jeffc/nrf52-watch-obsolete/packages/framework-arduinoadafruitnrf52/cores/nRF5/nordic/nrfx/mdk/nrf51_to_nrf52.h

/*

Copyright (c) 2010 - 2018, Nordic Semiconductor ASA All rights reserved.

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
1. Redistributions of source code must retain the above copyright notice, this
   list of conditions and the following disclaimer.

2. Redistributions in binary form must reproduce the above copyright
   notice, this list of conditions and the following disclaimer in the
   documentation and/or other materials provided with the distribution.

3. Neither the name of Nordic Semiconductor ASA nor the names of its
   contributors may be used to endorse or promote products derived from this
   software without specific prior written permission.

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
*/

#ifndef NRF51_TO_NRF52_H
#define NRF51_TO_NRF52_H

/*lint ++flb "Enter library region */

/* This file is given to prevent your SW from not compiling with the name changes between nRF51 and nRF52 devices.
 * It redefines the old nRF51 names into the new ones as long as the functionality is still supported. If the
 * functionality is gone, there old names are not defined, so compilation will fail. Note that also includes macros
 * from the nrf51_deprecated.h file. */


/* IRQ */
/* Several peripherals have been added to several indexes. Names of IRQ handlers and IRQ numbers have changed. */
#ifndef UART0_IRQHandler
    #define UART0_IRQHandler        UARTE0_UART0_IRQHandler
#endif
#ifndef SPI0_TWI0_IRQHandler
    #define SPI0_TWI0_IRQHandler    SPIM0_SPIS0_TWIM0_TWIS0_SPI0_TWI0_IRQHandler
#endif
#ifndef SPI1_TWI1_IRQHandler
    #define SPI1_TWI1_IRQHandler    SPIM1_SPIS1_TWIM1_TWIS1_SPI1_TWI1_IRQHandler
#endif
#ifndef ADC_IRQHandler
    #define ADC_IRQHandler          SAADC_IRQHandler
#endif
#ifndef LPCOMP_IRQHandler
    #define LPCOMP_IRQHandler       COMP_LPCOMP_IRQHandler
#endif
#ifndef SWI0_IRQHandler
    #define SWI0_IRQHandler         SWI0_EGU0_IRQHandler
#endif
#ifndef SWI1_IRQHandler
    #define SWI1_IRQHandler         SWI1_EGU1_IRQHandler
#endif
#ifndef SWI2_IRQHandler
    #define SWI2_IRQHandler         SWI2_EGU2_IRQHandler
#endif
#ifndef SWI3_IRQHandler
    #define SWI3_IRQHandler         SWI3_EGU3_IRQHandler
#endif
#ifndef SWI4_IRQHandler
    #define SWI4_IRQHandler         SWI4_EGU4_IRQHandler
#endif
#ifndef SWI5_IRQHandler
    #define SWI5_IRQHandler         SWI5_EGU5_IRQHandler
#endif

#ifndef UART0_IRQn
    #define UART0_IRQn              UARTE0_UART0_IRQn
#endif
#ifndef SPI0_TWI0_IRQn
    #define SPI0_TWI0_IRQn          SPIM0_SPIS0_TWIM0_TWIS0_SPI0_TWI0_IRQn
#endif
#ifndef SPI1_TWI1_IRQn
    #define SPI1_TWI1_IRQn          SPIM1_SPIS1_TWIM1_TWIS1_SPI1_TWI1_IRQn
#endif
#ifndef ADC_IRQn
    #define ADC_IRQn                SAADC_IRQn
#endif
#ifndef LPCOMP_IRQn
    #define LPCOMP_IRQn             COMP_LPCOMP_IRQn
#endif
#ifndef SWI0_IRQn
    #define SWI0_IRQn               SWI0_EGU0_IRQn
#endif
#ifndef SWI1_IRQn
    #define SWI1_IRQn               SWI1_EGU1_IRQn
#endif
#ifndef SWI2_IRQn
    #define SWI2_IRQn               SWI2_EGU2_IRQn
#endif
#ifndef SWI3_IRQn
    #define SWI3_IRQn               SWI3_EGU3_IRQn
#endif    
#ifndef SWI4_IRQn
    #define SWI4_IRQn               SWI4_EGU4_IRQn
#endif    
#ifndef SWI5_IRQn
    #define SWI5_IRQn               SWI5_EGU5_IRQn
#endif


/* UICR */
/* Register RBPCONF was renamed to APPROTECT. */
#ifndef RBPCONF
    #define RBPCONF     APPROTECT
#endif

#ifndef UICR_RBPCONF_PALL_Pos
    #define UICR_RBPCONF_PALL_Pos           UICR_APPROTECT_PALL_Pos
#endif
#ifndef UICR_RBPCONF_PALL_Msk
    #define UICR_RBPCONF_PALL_Msk           UICR_APPROTECT_PALL_Msk
#endif
#ifndef UICR_RBPCONF_PALL_Enabled
    #define UICR_RBPCONF_PALL_Enabled       UICR_APPROTECT_PALL_Enabled
#endif
#ifndef UICR_RBPCONF_PALL_Disabled
    #define UICR_RBPCONF_PALL_Disabled      UICR_APPROTECT_PALL_Disabled
#endif

/* GPIO */
/* GPIO port was renamed to P0. */
#ifndef NRF_GPIO
    #define NRF_GPIO        NRF_P0
#endif
#ifndef NRF_GPIO_BASE
    #define NRF_GPIO_BASE   NRF_P0_BASE
#endif

/* QDEC */
/* The registers PSELA, PSELB and PSELLED were restructured into a struct. */
#ifndef PSELLED
    #define PSELLED     PSEL.LED
#endif
#ifndef PSELA
    #define PSELA       PSEL.A
#endif
#ifndef PSELB
    #define PSELB       PSEL.B
#endif


/* SPIS */
/* The registers PSELSCK, PSELMISO, PSELMOSI, PSELCSN were restructured into a struct. */
#ifndef PSELSCK
    #define PSELSCK       PSEL.SCK
#endif
#ifndef PSELMISO
    #define PSELMISO      PSEL.MISO
#endif
#ifndef PSELMOSI
    #define PSELMOSI      PSEL.MOSI
#endif
#ifndef PSELCSN
    #define PSELCSN       PSEL.CSN
#endif    

/* The registers RXDPTR, MAXRX, AMOUNTRX were restructured into a struct */
#ifndef RXDPTR
    #define RXDPTR        RXD.PTR
#endif
#ifndef MAXRX
    #define MAXRX         RXD.MAXCNT
#endif
#ifndef AMOUNTRX
    #define AMOUNTRX      RXD.AMOUNT
#endif

#ifndef SPIS_MAXRX_MAXRX_Pos
    #define SPIS_MAXRX_MAXRX_Pos        SPIS_RXD_MAXCNT_MAXCNT_Pos
#endif
#ifndef SPIS_MAXRX_MAXRX_Msk
    #define SPIS_MAXRX_MAXRX_Msk        SPIS_RXD_MAXCNT_MAXCNT_Msk
#endif

#ifndef SPIS_AMOUNTRX_AMOUNTRX_Pos
    #define SPIS_AMOUNTRX_AMOUNTRX_Pos  SPIS_RXD_AMOUNT_AMOUNT_Pos
#endif
#ifndef SPIS_AMOUNTRX_AMOUNTRX_Msk
    #define SPIS_AMOUNTRX_AMOUNTRX_Msk  SPIS_RXD_AMOUNT_AMOUNT_Msk
#endif

/* The registers TXDPTR, MAXTX, AMOUNTTX were restructured into a struct */
#ifndef TXDPTR
    #define TXDPTR        TXD.PTR
#endif
#ifndef MAXTX
    #define MAXTX         TXD.MAXCNT
#endif
#ifndef AMOUNTTX
    #define AMOUNTTX      TXD.AMOUNT
#endif

#ifndef SPIS_MAXTX_MAXTX_Pos
    #define SPIS_MAXTX_MAXTX_Pos        SPIS_TXD_MAXCNT_MAXCNT_Pos
#endif
#ifndef SPIS_MAXTX_MAXTX_Msk
    #define SPIS_MAXTX_MAXTX_Msk        SPIS_TXD_MAXCNT_MAXCNT_Msk
#endif

#ifndef SPIS_AMOUNTTX_AMOUNTTX_Pos
    #define SPIS_AMOUNTTX_AMOUNTTX_Pos  SPIS_TXD_AMOUNT_AMOUNT_Pos
#endif
#ifndef SPIS_AMOUNTTX_AMOUNTTX_Msk
    #define SPIS_AMOUNTTX_AMOUNTTX_Msk  SPIS_TXD_AMOUNT_AMOUNT_Msk
#endif

/* MPU */
/* Part of MPU module was renamed BPROT, while the rest was eliminated. */
#ifndef NRF_MPU
    #define NRF_MPU     NRF_BPROT
#endif

/* Register DISABLEINDEBUG macros were affected. */
#ifndef MPU_DISABLEINDEBUG_DISABLEINDEBUG_Pos
    #define MPU_DISABLEINDEBUG_DISABLEINDEBUG_Pos       BPROT_DISABLEINDEBUG_DISABLEINDEBUG_Pos
#endif
#ifndef MPU_DISABLEINDEBUG_DISABLEINDEBUG_Msk
    #define MPU_DISABLEINDEBUG_DISABLEINDEBUG_Msk       BPROT_DISABLEINDEBUG_DISABLEINDEBUG_Msk
#endif
#ifndef MPU_DISABLEINDEBUG_DISABLEINDEBUG_Enabled
    #define MPU_DISABLEINDEBUG_DISABLEINDEBUG_Enabled   BPROT_DISABLEINDEBUG_DISABLEINDEBUG_Enabled
#endif
#ifndef MPU_DISABLEINDEBUG_DISABLEINDEBUG_Disabled
    #define MPU_DISABLEINDEBUG_DISABLEINDEBUG_Disabled  BPROT_DISABLEINDEBUG_DISABLEINDEBUG_Disabled
#endif

/* Registers PROTENSET0 and PROTENSET1 were affected and renamed as CONFIG0 and CONFIG1. */
#ifndef PROTENSET0
    #define PROTENSET0  CONFIG0
#endif
#ifndef PROTENSET1
    #define PROTENSET1  CONFIG1
#endif

#ifndef MPU_PROTENSET1_PROTREG63_Pos
    #define MPU_PROTENSET1_PROTREG63_Pos        BPROT_CONFIG1_REGION63_Pos
#endif
#ifndef MPU_PROTENSET1_PROTREG63_Msk
    #define MPU_PROTENSET1_PROTREG63_Msk        BPROT_CONFIG1_REGION63_Msk
#endif
#ifndef MPU_PROTENSET1_PROTREG63_Disabled
    #define MPU_PROTENSET1_PROTREG63_Disabled   BPROT_CONFIG1_REGION63_Disabled
#endif
#ifndef MPU_PROTENSET1_PROTREG63_Enabled
    #define MPU_PROTENSET1_PROTREG63_Enabled    BPROT_CONFIG1_REGION63_Enabled
#endif
#ifndef MPU_PROTENSET1_PROTREG63_Set
    #define MPU_PROTENSET1_PROTREG63_Set        BPROT_CONFIG1_REGION63_Enabled
#endif

#ifndef MPU_PROTENSET1_PROTREG62_Pos
    #define MPU_PROTENSET1_PROTREG62_Pos        BPROT_CONFIG1_REGION62_Pos
#endif
#ifndef MPU_PROTENSET1_PROTREG62_Msk
    #define MPU_PROTENSET1_PROTREG62_Msk        BPROT_CONFIG1_REGION62_Msk
#endif
#ifndef MPU_PROTENSET1_PROTREG62_Disabled
    #define MPU_PROTENSET1_PROTREG62_Disabled   BPROT_CONFIG1_REGION62_Disabled
#endif
#ifndef MPU_PROTENSET1_PROTREG62_Enabled
    #define MPU_PROTENSET1_PROTREG62_Enabled    BPROT_CONFIG1_REGION62_Enabled
#endif
#ifndef MPU_PROTENSET1_PROTREG62_Set
    #define MPU_PROTENSET1_PROTREG62_Set        BPROT_CONFIG1_REGION62_Enabled
#endif

#ifndef MPU_PROTENSET1_PROTREG61_Pos
    #define MPU_PROTENSET1_PROTREG61_Pos        BPROT_CONFIG1_REGION61_Pos
#endif
#ifndef MPU_PROTENSET1_PROTREG61_Msk
    #define MPU_PROTENSET1_PROTREG61_Msk        BPROT_CONFIG1_REGION61_Msk
#endif
#ifndef MPU_PROTENSET1_PROTREG61_Disabled
    #define MPU_PROTENSET1_PROTREG61_Disabled   BPROT_CONFIG1_REGION61_Disabled
#endif
#ifndef MPU_PROTENSET1_PROTREG61_Enabled
    #define MPU_PROTENSET1_PROTREG61_Enabled    BPROT_CONFIG1_REGION61_Enabled
#endif
#ifndef MPU_PROTENSET1_PROTREG61_Set
    #define MPU_PROTENSET1_PROTREG61_Set        BPROT_CONFIG1_REGION61_Enabled
#endif

#ifndef MPU_PROTENSET1_PROTREG60_Pos
    #define MPU_PROTENSET1_PROTREG60_Pos        BPROT_CONFIG1_REGION60_Pos
#endif
#ifndef MPU_PROTENSET1_PROTREG60_Msk
    #define MPU_PROTENSET1_PROTREG60_Msk        BPROT_CONFIG1_REGION60_Msk
#endif
#ifndef MPU_PROTENSET1_PROTREG60_Disabled
    #define MPU_PROTENSET1_PROTREG60_Disabled   BPROT_CONFIG1_REGION60_Disabled
#endif
#ifndef MPU_PROTENSET1_PROTREG60_Enabled
    #define MPU_PROTENSET1_PROTREG60_Enabled    BPROT_CONFIG1_REGION60_Enabled
#endif
#ifndef MPU_PROTENSET1_PROTREG60_Set
    #define MPU_PROTENSET1_PROTREG60_Set        BPROT_CONFIG1_REGION60_Enabled
#endif

#ifndef MPU_PROTENSET1_PROTREG59_Pos
    #define MPU_PROTENSET1_PROTREG59_Pos        BPROT_CONFIG1_REGION59_Pos
#endif
#ifndef MPU_PROTENSET1_PROTREG59_Msk
    #define MPU_PROTENSET1_PROTREG59_Msk        BPROT_CONFIG1_REGION59_Msk
#endif
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
#endif
#ifndef MPU_PROTENSET0_PROTREG2_Enabled
    #define MPU_PROTENSET0_PROTREG2_Enabled    BPROT_CONFIG0_REGION2_Enabled
#endif
#ifndef MPU_PROTENSET0_PROTREG2_Set
    #define MPU_PROTENSET0_PROTREG2_Set        BPROT_CONFIG0_REGION2_Enabled
#endif

#ifndef MPU_PROTENSET0_PROTREG1_Pos
    #define MPU_PROTENSET0_PROTREG1_Pos        BPROT_CONFIG0_REGION1_Pos
#endif
#ifndef MPU_PROTENSET0_PROTREG1_Msk
    #define MPU_PROTENSET0_PROTREG1_Msk        BPROT_CONFIG0_REGION1_Msk
#endif
#ifndef MPU_PROTENSET0_PROTREG1_Disabled
    #define MPU_PROTENSET0_PROTREG1_Disabled   BPROT_CONFIG0_REGION1_Disabled
#endif
#ifndef MPU_PROTENSET0_PROTREG1_Enabled
    #define MPU_PROTENSET0_PROTREG1_Enabled    BPROT_CONFIG0_REGION1_Enabled
#endif
#ifndef MPU_PROTENSET0_PROTREG1_Set
    #define MPU_PROTENSET0_PROTREG1_Set        BPROT_CONFIG0_REGION1_Enabled
#endif

#ifndef MPU_PROTENSET0_PROTREG0_Pos
    #define MPU_PROTENSET0_PROTREG0_Pos        BPROT_CONFIG0_REGION0_Pos
#endif
#ifndef MPU_PROTENSET0_PROTREG0_Msk
    #define MPU_PROTENSET0_PROTREG0_Msk        BPROT_CONFIG0_REGION0_Msk
#endif
#ifndef MPU_PROTENSET0_PROTREG0_Disabled
    #define MPU_PROTENSET0_PROTREG0_Disabled   BPROT_CONFIG0_REGION0_Disabled
#endif
#ifndef MPU_PROTENSET0_PROTREG0_Enabled
    #define MPU_PROTENSET0_PROTREG0_Enabled    BPROT_CONFIG0_REGION0_Enabled
#endif
#ifndef MPU_PROTENSET0_PROTREG0_Set
    #define MPU_PROTENSET0_PROTREG0_Set        BPROT_CONFIG0_REGION0_Enabled
#endif


/* From nrf51_deprecated.h */

/* NVMC */
/* The register ERASEPROTECTEDPAGE changed name to ERASEPCR0 in the documentation. */
#ifndef ERASEPROTECTEDPAGE
    #define ERASEPROTECTEDPAGE      ERASEPCR0
#endif    


/* IRQ */
/* COMP module was eliminated. Adapted to nrf52 headers. */
#ifndef LPCOMP_COMP_IRQHandler
    #define LPCOMP_COMP_IRQHandler  COMP_LPCOMP_IRQHandler
#endif
#ifndef LPCOMP_COMP_IRQn
    #define LPCOMP_COMP_IRQn        COMP_LPCOMP_IRQn
#endif


/* REFSEL register redefined enumerated values and added some more. */
#ifndef LPCOMP_REFSEL_REFSEL_SupplyOneEighthPrescaling
    #define LPCOMP_REFSEL_REFSEL_SupplyOneEighthPrescaling          LPCOMP_REFSEL_REFSEL_Ref1_8Vdd
#endif
#ifndef LPCOMP_REFSEL_REFSEL_SupplyTwoEighthsPrescaling
    #define LPCOMP_REFSEL_REFSEL_SupplyTwoEighthsPrescaling         LPCOMP_REFSEL_REFSEL_Ref2_8Vdd
#endif
#ifndef LPCOMP_REFSEL_REFSEL_SupplyThreeEighthsPrescaling
    #define LPCOMP_REFSEL_REFSEL_SupplyThreeEighthsPrescaling       LPCOMP_REFSEL_REFSEL_Ref3_8Vdd
#endif
#ifndef LPCOMP_REFSEL_REFSEL_SupplyFourEighthsPrescaling
    #define LPCOMP_REFSEL_REFSEL_SupplyFourEighthsPrescaling        LPCOMP_REFSEL_REFSEL_Ref4_8Vdd
#endif
#ifndef LPCOMP_REFSEL_REFSEL_SupplyFiveEighthsPrescaling
    #define LPCOMP_REFSEL_REFSEL_SupplyFiveEighthsPrescaling        LPCOMP_REFSEL_REFSEL_Ref5_8Vdd
#endif
#ifndef LPCOMP_REFSEL_REFSEL_SupplySixEighthsPrescaling
    #define LPCOMP_REFSEL_REFSEL_SupplySixEighthsPrescaling         LPCOMP_REFSEL_REFSEL_Ref6_8Vdd
#endif
#ifndef LPCOMP_REFSEL_REFSEL_SupplySevenEighthsPrescaling
    #define LPCOMP_REFSEL_REFSEL_SupplySevenEighthsPrescaling       LPCOMP_REFSEL_REFSEL_Ref7_8Vdd
#endif

/* RADIO */
/* The name of the field SKIPADDR was corrected. Old macros added for compatibility. */
#ifndef RADIO_CRCCNF_SKIP_ADDR_Pos
    #define RADIO_CRCCNF_SKIP_ADDR_Pos      RADIO_CRCCNF_SKIPADDR_Pos
#endif
#ifndef RADIO_CRCCNF_SKIP_ADDR_Msk
    #define RADIO_CRCCNF_SKIP_ADDR_Msk      RADIO_CRCCNF_SKIPADDR_Msk
#endif
#ifndef RADIO_CRCCNF_SKIP_ADDR_Include
    #define RADIO_CRCCNF_SKIP_ADDR_Include  RADIO_CRCCNF_SKIPADDR_Include
#endif
#ifndef RADIO_CRCCNF_SKIP_ADDR_Skip
    #define RADIO_CRCCNF_SKIP_ADDR_Skip     RADIO_CRCCNF_SKIPADDR_Skip
#endif


/* FICR */
/* The registers FICR.DEVICEID0 and FICR.DEVICEID1 were renamed into an array. */
#ifndef DEVICEID0
    #define DEVICEID0       DEVICEID[0]
#endif
#ifndef DEVICEID1
    #define DEVICEID1       DEVICEID[1]
#endif

/* The registers FICR.ER0, FICR.ER1, FICR.ER2 and FICR.ER3 were renamed into an array. */
#ifndef ER0
    #define ER0             ER[0]
#endif
#ifndef ER1
    #define ER1             ER[1]
#endif
#ifndef ER2
    #define ER2             ER[2]
#endif
#ifndef ER3
    #define ER3             ER[3]
#endif

/* The registers FICR.IR0, FICR.IR1, FICR.IR2 and FICR.IR3 were renamed into an array. */
#ifndef IR0
    #define IR0             IR[0]
#endif
#ifndef IR1
    #define IR1             IR[1]
#endif
#ifndef IR2
    #define IR2             IR[2]
#endif
#ifndef IR3
    #define IR3             IR[3]
#endif

/* The registers FICR.DEVICEADDR0 and FICR.DEVICEADDR1 were renamed into an array. */
#ifndef DEVICEADDR0
    #define DEVICEADDR0     DEVICEADDR[0]
#endif
#ifndef DEVICEADDR1
    #define DEVICEADDR1     DEVICEADDR[1]
#endif


/* PPI */
/* The tasks PPI.TASKS_CHGxEN and PPI.TASKS_CHGxDIS were renamed into an array of structs. */
#ifndef TASKS_CHG0EN
    #define TASKS_CHG0EN     TASKS_CHG[0].EN
#endif
#ifndef TASKS_CHG0DIS
    #define TASKS_CHG0DIS    TASKS_CHG[0].DIS
#endif
#ifndef TASKS_CHG1EN
    #define TASKS_CHG1EN     TASKS_CHG[1].EN
#endif
#ifndef TASKS_CHG1DIS
    #define TASKS_CHG1DIS    TASKS_CHG[1].DIS
#endif
#ifndef TASKS_CHG2EN
    #define TASKS_CHG2EN     TASKS_CHG[2].EN
#endif
#ifndef TASKS_CHG2DIS
    #define TASKS_CHG2DIS    TASKS_CHG[2].DIS
#endif
#ifndef TASKS_CHG3EN
    #define TASKS_CHG3EN     TASKS_CHG[3].EN
#endif
#ifndef TASKS_CHG3DIS
    #define TASKS_CHG3DIS    TASKS_CHG[3].DIS
#endif

/* The registers PPI.CHx_EEP and PPI.CHx_TEP were renamed into an array of structs. */
#ifndef CH0_EEP
    #define CH0_EEP          CH[0].EEP
#endif
#ifndef CH0_TEP
    #define CH0_TEP          CH[0].TEP
#endif
#ifndef CH1_EEP
    #define CH1_EEP          CH[1].EEP
#endif
#ifndef CH1_TEP
    #define CH1_TEP          CH[1].TEP
#endif
#ifndef CH2_EEP
    #define CH2_EEP          CH[2].EEP
#endif
#ifndef CH2_TEP
    #define CH2_TEP          CH[2].TEP
#endif
#ifndef CH3_EEP
    #define CH3_EEP          CH[3].EEP
#endif
#ifndef CH3_TEP
    #define CH3_TEP          CH[3].TEP
#endif
#ifndef CH4_EEP
    #define CH4_EEP          CH[4].EEP
#endif
#ifndef CH4_TEP
    #define CH4_TEP          CH[4].TEP
#endif
#ifndef CH5_EEP
    #define CH5_EEP          CH[5].EEP
#endif
#ifndef CH5_TEP
    #define CH5_TEP          CH[5].TEP
#endif
#ifndef CH6_EEP
    #define CH6_EEP          CH[6].EEP
#endif
#ifndef CH6_TEP
    #define CH6_TEP          CH[6].TEP
#endif 
#ifndef CH7_EEP
    #define CH7_EEP          CH[7].EEP
#endif
#ifndef CH7_TEP
    #define CH7_TEP          CH[7].TEP
#endif
#ifndef CH8_EEP
    #define CH8_EEP          CH[8].EEP
#endif
#ifndef CH8_TEP
    #define CH8_TEP          CH[8].TEP
#endif
#ifndef CH9_EEP
    #define CH9_EEP          CH[9].EEP
#endif
#ifndef CH9_TEP
    #define CH9_TEP          CH[9].TEP
#endif
#ifndef CH10_EEP
    #define CH10_EEP         CH[10].EEP
#endif
#ifndef CH10_TEP
    #define CH10_TEP         CH[10].TEP
#endif
#ifndef CH11_EEP
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
#endif
#ifndef PPI_CHG3_CH0_Excluded
    #define PPI_CHG3_CH0_Excluded   PPI_CHG_CH0_Excluded
#endif
#ifndef PPI_CHG3_CH0_Included
    #define PPI_CHG3_CH0_Included   PPI_CHG_CH0_Included
#endif



/*lint --flb "Leave library region" */

#endif /* NRF51_TO_NRF52_H */
