jeffc/nrf52-watch-obsolete/packages/framework-arduinoadafruitnrf52/cores/nRF5/nordic/softdevice/s132_nrf52_6.1.1_API/include/ble_gap.h

/*
 * Copyright (c) 2011 - 2018, Nordic Semiconductor ASA
 * All rights reserved.
 *
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
 * 3. Neither the name of Nordic Semiconductor ASA nor the names of its
 *    contributors may be used to endorse or promote products derived from this
 *    software without specific prior written permission.
 *
 * 4. This software, with or without modification, must only be used with a
 *    Nordic Semiconductor ASA integrated circuit.
 *
 * 5. Any software provided in binary form under this license must not be reverse
 *    engineered, decompiled, modified and/or disassembled.
 *
 * THIS SOFTWARE IS PROVIDED BY NORDIC SEMICONDUCTOR ASA "AS IS" AND ANY EXPRESS
 * OR IMPLIED WARRANTIES, INCLUDING, BUT NOT LIMITED TO, THE IMPLIED WARRANTIES
 * OF MERCHANTABILITY, NONINFRINGEMENT, AND FITNESS FOR A PARTICULAR PURPOSE ARE
 * DISCLAIMED. IN NO EVENT SHALL NORDIC SEMICONDUCTOR ASA OR CONTRIBUTORS BE
 * LIABLE FOR ANY DIRECT, INDIRECT, INCIDENTAL, SPECIAL, EXEMPLARY, OR
 * CONSEQUENTIAL DAMAGES (INCLUDING, BUT NOT LIMITED TO, PROCUREMENT OF SUBSTITUTE
 * GOODS OR SERVICES; LOSS OF USE, DATA, OR PROFITS; OR BUSINESS INTERRUPTION)
 * HOWEVER CAUSED AND ON ANY THEORY OF LIABILITY, WHETHER IN CONTRACT, STRICT
 * LIABILITY, OR TORT (INCLUDING NEGLIGENCE OR OTHERWISE) ARISING IN ANY WAY OUT
 * OF THE USE OF THIS SOFTWARE, EVEN IF ADVISED OF THE POSSIBILITY OF SUCH DAMAGE.
 */

/**
  @addtogroup BLE_GAP Generic Access Profile (GAP)
  @{
  @brief Definitions and prototypes for the GAP interface.
 */

#ifndef BLE_GAP_H__
#define BLE_GAP_H__

#include <stdint.h>
#include "nrf_svc.h"
#include "nrf_error.h"
#include "ble_hci.h"
#include "ble_ranges.h"
#include "ble_types.h"
#include "ble_err.h"

#ifdef __cplusplus
extern "C" {
#endif

/**@addtogroup BLE_GAP_ENUMERATIONS Enumerations
 * @{ */

/**@brief GAP API SVC numbers.
 */
enum BLE_GAP_SVCS
{
  SD_BLE_GAP_ADDR_SET              = BLE_GAP_SVC_BASE,       /**< Set own Bluetooth Address. */
  SD_BLE_GAP_ADDR_GET              = BLE_GAP_SVC_BASE + 1,   /**< Get own Bluetooth Address. */
  SD_BLE_GAP_WHITELIST_SET         = BLE_GAP_SVC_BASE + 2,   /**< Set active whitelist. */
  SD_BLE_GAP_DEVICE_IDENTITIES_SET = BLE_GAP_SVC_BASE + 3,   /**< Set device identity list. */
  SD_BLE_GAP_PRIVACY_SET           = BLE_GAP_SVC_BASE + 4,   /**< Set Privacy settings*/
  SD_BLE_GAP_PRIVACY_GET           = BLE_GAP_SVC_BASE + 5,   /**< Get Privacy settings*/
  SD_BLE_GAP_ADV_SET_CONFIGURE     = BLE_GAP_SVC_BASE + 6,   /**< Configure an advertising set. */
  SD_BLE_GAP_ADV_START             = BLE_GAP_SVC_BASE + 7,   /**< Start Advertising. */
  SD_BLE_GAP_ADV_STOP              = BLE_GAP_SVC_BASE + 8,   /**< Stop Advertising. */
  SD_BLE_GAP_CONN_PARAM_UPDATE     = BLE_GAP_SVC_BASE + 9,   /**< Connection Parameter Update. */
  SD_BLE_GAP_DISCONNECT            = BLE_GAP_SVC_BASE + 10,  /**< Disconnect. */
  SD_BLE_GAP_TX_POWER_SET          = BLE_GAP_SVC_BASE + 11,  /**< Set TX Power. */
  SD_BLE_GAP_APPEARANCE_SET        = BLE_GAP_SVC_BASE + 12,  /**< Set Appearance. */
  SD_BLE_GAP_APPEARANCE_GET        = BLE_GAP_SVC_BASE + 13,  /**< Get Appearance. */
  SD_BLE_GAP_PPCP_SET              = BLE_GAP_SVC_BASE + 14,  /**< Set PPCP. */
  SD_BLE_GAP_PPCP_GET              = BLE_GAP_SVC_BASE + 15,  /**< Get PPCP. */
  SD_BLE_GAP_DEVICE_NAME_SET       = BLE_GAP_SVC_BASE + 16,  /**< Set Device Name. */
  SD_BLE_GAP_DEVICE_NAME_GET       = BLE_GAP_SVC_BASE + 17,  /**< Get Device Name. */
  SD_BLE_GAP_AUTHENTICATE          = BLE_GAP_SVC_BASE + 18,  /**< Initiate Pairing/Bonding. */
  SD_BLE_GAP_SEC_PARAMS_REPLY      = BLE_GAP_SVC_BASE + 19,  /**< Reply with Security Parameters. */
  SD_BLE_GAP_AUTH_KEY_REPLY        = BLE_GAP_SVC_BASE + 20,  /**< Reply with an authentication key. */
  SD_BLE_GAP_LESC_DHKEY_REPLY      = BLE_GAP_SVC_BASE + 21,  /**< Reply with an LE Secure Connections DHKey. */
  SD_BLE_GAP_KEYPRESS_NOTIFY       = BLE_GAP_SVC_BASE + 22,  /**< Notify of a keypress during an authentication procedure. */
  SD_BLE_GAP_LESC_OOB_DATA_GET     = BLE_GAP_SVC_BASE + 23,  /**< Get the local LE Secure Connections OOB data. */
  SD_BLE_GAP_LESC_OOB_DATA_SET     = BLE_GAP_SVC_BASE + 24,  /**< Set the remote LE Secure Connections OOB data. */
  SD_BLE_GAP_ENCRYPT               = BLE_GAP_SVC_BASE + 25,  /**< Initiate encryption procedure. */
  SD_BLE_GAP_SEC_INFO_REPLY        = BLE_GAP_SVC_BASE + 26,  /**< Reply with Security Information. */
  SD_BLE_GAP_CONN_SEC_GET          = BLE_GAP_SVC_BASE + 27,  /**< Obtain connection security level. */
  SD_BLE_GAP_RSSI_START            = BLE_GAP_SVC_BASE + 28,  /**< Start reporting of changes in RSSI. */
  SD_BLE_GAP_RSSI_STOP             = BLE_GAP_SVC_BASE + 29,  /**< Stop reporting of changes in RSSI. */
  SD_BLE_GAP_SCAN_START            = BLE_GAP_SVC_BASE + 30,  /**< Start Scanning. */
  SD_BLE_GAP_SCAN_STOP             = BLE_GAP_SVC_BASE + 31,  /**< Stop Scanning. */
  SD_BLE_GAP_CONNECT               = BLE_GAP_SVC_BASE + 32,  /**< Connect. */
  SD_BLE_GAP_CONNECT_CANCEL        = BLE_GAP_SVC_BASE + 33,  /**< Cancel ongoing connection procedure. */
  SD_BLE_GAP_RSSI_GET              = BLE_GAP_SVC_BASE + 34,  /**< Get the last RSSI sample. */
  SD_BLE_GAP_PHY_UPDATE            = BLE_GAP_SVC_BASE + 35,  /**< Initiate or respond to a PHY Update Procedure. */
  SD_BLE_GAP_DATA_LENGTH_UPDATE    = BLE_GAP_SVC_BASE + 36,  /**< Initiate or respond to a Data Length Update Procedure. */
  SD_BLE_GAP_QOS_CHANNEL_SURVEY_START  = BLE_GAP_SVC_BASE + 37, /**< Start Quality of Service (QoS) channel survey module. */
  SD_BLE_GAP_QOS_CHANNEL_SURVEY_STOP   = BLE_GAP_SVC_BASE + 38, /**< Stop Quality of Service (QoS) channel survey module. */
  SD_BLE_GAP_ADV_ADDR_GET          = BLE_GAP_SVC_BASE + 39, /**< Get the Address used on air while Advertising. */
};

/**@brief GAP Event IDs.
 * IDs that uniquely identify an event coming from the stack to the application.
 */
enum BLE_GAP_EVTS
{
  BLE_GAP_EVT_CONNECTED                   = BLE_GAP_EVT_BASE,       /**< Connected to peer.                              \n See @ref ble_gap_evt_connected_t             */
  BLE_GAP_EVT_DISCONNECTED                = BLE_GAP_EVT_BASE + 1,   /**< Disconnected from peer.                         \n See @ref ble_gap_evt_disconnected_t.         */
  BLE_GAP_EVT_CONN_PARAM_UPDATE           = BLE_GAP_EVT_BASE + 2,   /**< Connection Parameters updated.                  \n See @ref ble_gap_evt_conn_param_update_t.    */
  BLE_GAP_EVT_SEC_PARAMS_REQUEST          = BLE_GAP_EVT_BASE + 3,   /**< Request to provide security parameters.         \n Reply with @ref sd_ble_gap_sec_params_reply.  \n See @ref ble_gap_evt_sec_params_request_t. */
  BLE_GAP_EVT_SEC_INFO_REQUEST            = BLE_GAP_EVT_BASE + 4,   /**< Request to provide security information.        \n Reply with @ref sd_ble_gap_sec_info_reply.    \n See @ref ble_gap_evt_sec_info_request_t.   */
  BLE_GAP_EVT_PASSKEY_DISPLAY             = BLE_GAP_EVT_BASE + 5,   /**< Request to display a passkey to the user.       \n In LESC Numeric Comparison, reply with @ref sd_ble_gap_auth_key_reply. \n See @ref ble_gap_evt_passkey_display_t. */
  BLE_GAP_EVT_KEY_PRESSED                 = BLE_GAP_EVT_BASE + 6,   /**< Notification of a keypress on the remote device.\n See @ref ble_gap_evt_key_pressed_t           */
  BLE_GAP_EVT_AUTH_KEY_REQUEST            = BLE_GAP_EVT_BASE + 7,   /**< Request to provide an authentication key.       \n Reply with @ref sd_ble_gap_auth_key_reply.    \n See @ref ble_gap_evt_auth_key_request_t.   */
  BLE_GAP_EVT_LESC_DHKEY_REQUEST          = BLE_GAP_EVT_BASE + 8,   /**< Request to calculate an LE Secure Connections DHKey. \n Reply with @ref sd_ble_gap_lesc_dhkey_reply.  \n See @ref ble_gap_evt_lesc_dhkey_request_t */
  BLE_GAP_EVT_AUTH_STATUS                 = BLE_GAP_EVT_BASE + 9,   /**< Authentication procedure completed with status. \n See @ref ble_gap_evt_auth_status_t.          */
  BLE_GAP_EVT_CONN_SEC_UPDATE             = BLE_GAP_EVT_BASE + 10,  /**< Connection security updated.                    \n See @ref ble_gap_evt_conn_sec_update_t.      */
  BLE_GAP_EVT_TIMEOUT                     = BLE_GAP_EVT_BASE + 11,  /**< Timeout expired.                                \n See @ref ble_gap_evt_timeout_t.              */
  BLE_GAP_EVT_RSSI_CHANGED                = BLE_GAP_EVT_BASE + 12,  /**< RSSI report.                                    \n See @ref ble_gap_evt_rssi_changed_t.         */
  BLE_GAP_EVT_ADV_REPORT                  = BLE_GAP_EVT_BASE + 13,  /**< Advertising report.                             \n See @ref ble_gap_evt_adv_report_t.           */
  BLE_GAP_EVT_SEC_REQUEST                 = BLE_GAP_EVT_BASE + 14,  /**< Security Request.                               \n See @ref ble_gap_evt_sec_request_t.          */
  BLE_GAP_EVT_CONN_PARAM_UPDATE_REQUEST   = BLE_GAP_EVT_BASE + 15,  /**< Connection Parameter Update Request.            \n Reply with @ref sd_ble_gap_conn_param_update. \n See @ref ble_gap_evt_conn_param_update_request_t. */
  BLE_GAP_EVT_SCAN_REQ_REPORT             = BLE_GAP_EVT_BASE + 16,  /**< Scan request report.                            \n See @ref ble_gap_evt_scan_req_report_t. */
  BLE_GAP_EVT_PHY_UPDATE_REQUEST          = BLE_GAP_EVT_BASE + 17,  /**< PHY Update Request.                             \n Reply with @ref sd_ble_gap_phy_update. \n See @ref ble_gap_evt_phy_update_request_t. */
  BLE_GAP_EVT_PHY_UPDATE                  = BLE_GAP_EVT_BASE + 18,  /**< PHY Update Procedure is complete.               \n See @ref ble_gap_evt_phy_update_t.           */
  BLE_GAP_EVT_DATA_LENGTH_UPDATE_REQUEST = BLE_GAP_EVT_BASE + 19,   /**< Data Length Update Request.                     \n Reply with @ref sd_ble_gap_data_length_update.\n See @ref ble_gap_evt_data_length_update_request_t. */
  BLE_GAP_EVT_DATA_LENGTH_UPDATE         = BLE_GAP_EVT_BASE + 20,   /**< LL Data Channel PDU payload length updated.     \n See @ref ble_gap_evt_data_length_update_t. */
  BLE_GAP_EVT_QOS_CHANNEL_SURVEY_REPORT  = BLE_GAP_EVT_BASE + 21,   /**< Channel survey report.                          \n See @ref ble_gap_evt_qos_channel_survey_report_t. */
  BLE_GAP_EVT_ADV_SET_TERMINATED         = BLE_GAP_EVT_BASE + 22,   /**< Advertising set terminated.                     \n See @ref ble_gap_evt_adv_set_terminated_t. */
};

/**@brief GAP Option IDs.
 * IDs that uniquely identify a GAP option.
 */
enum BLE_GAP_OPTS
{
  BLE_GAP_OPT_CH_MAP                 = BLE_GAP_OPT_BASE,       /**< Channel Map. @ref ble_gap_opt_ch_map_t  */
  BLE_GAP_OPT_LOCAL_CONN_LATENCY     = BLE_GAP_OPT_BASE + 1,   /**< Local connection latency. @ref ble_gap_opt_local_conn_latency_t */
  BLE_GAP_OPT_PASSKEY                = BLE_GAP_OPT_BASE + 2,   /**< Set passkey. @ref ble_gap_opt_passkey_t */
  BLE_GAP_OPT_COMPAT_MODE_1          = BLE_GAP_OPT_BASE + 3,   /**< Compatibility mode. @ref ble_gap_opt_compat_mode_1_t */
  BLE_GAP_OPT_AUTH_PAYLOAD_TIMEOUT   = BLE_GAP_OPT_BASE + 4,   /**< Set Authenticated payload timeout. @ref ble_gap_opt_auth_payload_timeout_t */
  BLE_GAP_OPT_SLAVE_LATENCY_DISABLE  = BLE_GAP_OPT_BASE + 5,   /**< Disable slave latency. @ref ble_gap_opt_slave_latency_disable_t */
};

/**@brief GAP Configuration IDs.
 *
 * IDs that uniquely identify a GAP configuration.
 */
enum BLE_GAP_CFGS
{
  BLE_GAP_CFG_ROLE_COUNT    = BLE_GAP_CFG_BASE,     /**< Role count configuration.  */
  BLE_GAP_CFG_DEVICE_NAME   = BLE_GAP_CFG_BASE + 1, /**< Device name configuration. */
};

/**@brief GAP TX Power roles.
 */
enum BLE_GAP_TX_POWER_ROLES
{
  BLE_GAP_TX_POWER_ROLE_ADV       = 1,           /**< Advertiser role. */
  BLE_GAP_TX_POWER_ROLE_SCAN_INIT = 2,           /**< Scanner and initiator role. */
  BLE_GAP_TX_POWER_ROLE_CONN      = 3,           /**< Connection role. */
};

/** @} */

/**@addtogroup BLE_GAP_DEFINES Defines
 * @{ */

/**@defgroup BLE_ERRORS_GAP SVC return values specific to GAP
 * @{ */
#define BLE_ERROR_GAP_UUID_LIST_MISMATCH            (NRF_GAP_ERR_BASE + 0x000)  /**< UUID list does not contain an integral number of UUIDs. */
#define BLE_ERROR_GAP_DISCOVERABLE_WITH_WHITELIST   (NRF_GAP_ERR_BASE + 0x001)  /**< Use of Whitelist not permitted with discoverable advertising. */
#define BLE_ERROR_GAP_INVALID_BLE_ADDR              (NRF_GAP_ERR_BASE + 0x002)  /**< The upper two bits of the address do not correspond to the specified address type. */
#define BLE_ERROR_GAP_WHITELIST_IN_USE              (NRF_GAP_ERR_BASE + 0x003)  /**< Attempt to modify the whitelist while already in use by another operation. */
#define BLE_ERROR_GAP_DEVICE_IDENTITIES_IN_USE      (NRF_GAP_ERR_BASE + 0x004)  /**< Attempt to modify the device identity list while already in use by another operation. */
#define BLE_ERROR_GAP_DEVICE_IDENTITIES_DUPLICATE   (NRF_GAP_ERR_BASE + 0x005)  /**< The device identity list contains entries with duplicate identity addresses. */
/**@} */


/**@defgroup BLE_GAP_ROLES GAP Roles
 * @{ */
#define BLE_GAP_ROLE_INVALID     0x0            /**< Invalid Role. */
#define BLE_GAP_ROLE_PERIPH      0x1            /**< Peripheral Role. */
#define BLE_GAP_ROLE_CENTRAL     0x2            /**< Central Role. */
/**@} */


/**@defgroup BLE_GAP_TIMEOUT_SOURCES GAP Timeout sources
 * @{ */
#define BLE_GAP_TIMEOUT_SRC_SCAN                       0x01 /**< Scanning timeout. */
#define BLE_GAP_TIMEOUT_SRC_CONN                       0x02 /**< Connection timeout. */
#define BLE_GAP_TIMEOUT_SRC_AUTH_PAYLOAD               0x03 /**< Authenticated payload timeout. */
/**@} */


/**@defgroup BLE_GAP_ADDR_TYPES GAP Address types
 * @{ */
#define BLE_GAP_ADDR_TYPE_PUBLIC                        0x00 /**< Public (identity) address.*/
#define BLE_GAP_ADDR_TYPE_RANDOM_STATIC                 0x01 /**< Random static (identity) address. */
#define BLE_GAP_ADDR_TYPE_RANDOM_PRIVATE_RESOLVABLE     0x02 /**< Random private resolvable address. */
#define BLE_GAP_ADDR_TYPE_RANDOM_PRIVATE_NON_RESOLVABLE 0x03 /**< Random private non-resolvable address. */
#define BLE_GAP_ADDR_TYPE_ANONYMOUS                     0x7F /**< An advertiser may advertise without its address.
                                                                  This type of advertising is called anonymous. */
/**@} */


/**@brief The default interval in seconds at which a private address is refreshed.  */
#define BLE_GAP_DEFAULT_PRIVATE_ADDR_CYCLE_INTERVAL_S (900) /* 15 minutes. */
/**@brief The maximum interval in seconds at which a private address can be refreshed.  */
#define BLE_GAP_MAX_PRIVATE_ADDR_CYCLE_INTERVAL_S     (41400) /* 11 hours 30 minutes. */


/** @brief BLE address length. */
#define BLE_GAP_ADDR_LEN (6)

/**@defgroup BLE_GAP_PRIVACY_MODES Privacy modes
 * @{ */
#define BLE_GAP_PRIVACY_MODE_OFF                       0x00 /**< Device will send and accept its identity address for its own address. */
#define BLE_GAP_PRIVACY_MODE_DEVICE_PRIVACY            0x01 /**< Device will send and accept only private addresses for its own address. */
#define BLE_GAP_PRIVACY_MODE_NETWORK_PRIVACY           0x02 /**< Device will send and accept only private addresses for its own address,
                                                                 and will not accept a peer using identity address as sender address when
                                                                 the peer IRK is exchanged, non-zero and added to the identity list. */
/**@} */

/** @brief Invalid power level. */
#define BLE_GAP_POWER_LEVEL_INVALID     127

/** @brief Advertising set handle not set. */
#define BLE_GAP_ADV_SET_HANDLE_NOT_SET (0xFF)

/** @brief The default number of advertising sets. */
#define BLE_GAP_ADV_SET_COUNT_DEFAULT   (1)

/** @brief The maximum number of advertising sets supported by this SoftDevice. */
#define BLE_GAP_ADV_SET_COUNT_MAX       (1)

/**@defgroup BLE_GAP_ADV_SET_DATA_SIZES Advertising data sizes.
 * @{ */
#define BLE_GAP_ADV_SET_DATA_SIZE_MAX                    (31)   /**< Maximum data length for an advertising set.
                                                                     If more advertising data is required, use extended advertising instead. */
#define BLE_GAP_ADV_SET_DATA_SIZE_EXTENDED_MAX_SUPPORTED (255)  /**< Maximum supported data length for an extended advertising set. */

#define BLE_GAP_ADV_SET_DATA_SIZE_EXTENDED_CONNECTABLE_MAX_SUPPORTED (238) /**< Maximum supported data length for an extended connectable advertising set. */
/**@}. */

/** @brief Set ID not available in advertising report. */
#define BLE_GAP_ADV_REPORT_SET_ID_NOT_AVAILABLE                    0xFF

/**@defgroup BLE_GAP_EVT_ADV_SET_TERMINATED_REASON GAP Advertising Set Terminated reasons
 * @{ */
#define BLE_GAP_EVT_ADV_SET_TERMINATED_REASON_TIMEOUT              0x01  /**< Timeout value reached. */
#define BLE_GAP_EVT_ADV_SET_TERMINATED_REASON_LIMIT_REACHED        0x02  /**< @ref ble_gap_adv_params_t::max_adv_evts was reached. */
/**@} */

/**@defgroup BLE_GAP_AD_TYPE_DEFINITIONS GAP Advertising and Scan Response Data format
 * @note Found at https://www.bluetooth.org/Technical/AssignedNumbers/generic_access_profile.htm
 * @{ */
#define BLE_GAP_AD_TYPE_FLAGS                               0x01 /**< Flags for discoverability. */
#define BLE_GAP_AD_TYPE_16BIT_SERVICE_UUID_MORE_AVAILABLE   0x02 /**< Partial list of 16 bit service UUIDs. */
#define BLE_GAP_AD_TYPE_16BIT_SERVICE_UUID_COMPLETE         0x03 /**< Complete list of 16 bit service UUIDs. */
#define BLE_GAP_AD_TYPE_32BIT_SERVICE_UUID_MORE_AVAILABLE   0x04 /**< Partial list of 32 bit service UUIDs. */
#define BLE_GAP_AD_TYPE_32BIT_SERVICE_UUID_COMPLETE         0x05 /**< Complete list of 32 bit service UUIDs. */
#define BLE_GAP_AD_TYPE_128BIT_SERVICE_UUID_MORE_AVAILABLE  0x06 /**< Partial list of 128 bit service UUIDs. */
#define BLE_GAP_AD_TYPE_128BIT_SERVICE_UUID_COMPLETE        0x07 /**< Complete list of 128 bit service UUIDs. */
#define BLE_GAP_AD_TYPE_SHORT_LOCAL_NAME                    0x08 /**< Short local device name. */
#define BLE_GAP_AD_TYPE_COMPLETE_LOCAL_NAME                 0x09 /**< Complete local device name. */
#define BLE_GAP_AD_TYPE_TX_POWER_LEVEL                      0x0A /**< Transmit power level. */
#define BLE_GAP_AD_TYPE_CLASS_OF_DEVICE                     0x0D /**< Class of device. */
#define BLE_GAP_AD_TYPE_SIMPLE_PAIRING_HASH_C               0x0E /**< Simple Pairing Hash C. */
#define BLE_GAP_AD_TYPE_SIMPLE_PAIRING_RANDOMIZER_R         0x0F /**< Simple Pairing Randomizer R. */
#define BLE_GAP_AD_TYPE_SECURITY_MANAGER_TK_VALUE           0x10 /**< Security Manager TK Value. */
#define BLE_GAP_AD_TYPE_SECURITY_MANAGER_OOB_FLAGS          0x11 /**< Security Manager Out Of Band Flags. */
#define BLE_GAP_AD_TYPE_SLAVE_CONNECTION_INTERVAL_RANGE     0x12 /**< Slave Connection Interval Range. */
#define BLE_GAP_AD_TYPE_SOLICITED_SERVICE_UUIDS_16BIT       0x14 /**< List of 16-bit Service Solicitation UUIDs. */
#define BLE_GAP_AD_TYPE_SOLICITED_SERVICE_UUIDS_128BIT      0x15 /**< List of 128-bit Service Solicitation UUIDs. */
#define BLE_GAP_AD_TYPE_SERVICE_DATA                        0x16 /**< Service Data - 16-bit UUID. */
#define BLE_GAP_AD_TYPE_PUBLIC_TARGET_ADDRESS               0x17 /**< Public Target Address. */
#define BLE_GAP_AD_TYPE_RANDOM_TARGET_ADDRESS               0x18 /**< Random Target Address. */
#define BLE_GAP_AD_TYPE_APPEARANCE                          0x19 /**< Appearance. */
#define BLE_GAP_AD_TYPE_ADVERTISING_INTERVAL                0x1A /**< Advertising Interval. */
#define BLE_GAP_AD_TYPE_LE_BLUETOOTH_DEVICE_ADDRESS         0x1B /**< LE Bluetooth Device Address. */
#define BLE_GAP_AD_TYPE_LE_ROLE                             0x1C /**< LE Role. */
#define BLE_GAP_AD_TYPE_SIMPLE_PAIRING_HASH_C256            0x1D /**< Simple Pairing Hash C-256. */
#define BLE_GAP_AD_TYPE_SIMPLE_PAIRING_RANDOMIZER_R256      0x1E /**< Simple Pairing Randomizer R-256. */
#define BLE_GAP_AD_TYPE_SERVICE_DATA_32BIT_UUID             0x20 /**< Service Data - 32-bit UUID. */
#define BLE_GAP_AD_TYPE_SERVICE_DATA_128BIT_UUID            0x21 /**< Service Data - 128-bit UUID. */
#define BLE_GAP_AD_TYPE_LESC_CONFIRMATION_VALUE             0x22 /**< LE Secure Connections Confirmation Value */
#define BLE_GAP_AD_TYPE_LESC_RANDOM_VALUE                   0x23 /**< LE Secure Connections Random Value */
#define BLE_GAP_AD_TYPE_URI                                 0x24 /**< URI */
#define BLE_GAP_AD_TYPE_3D_INFORMATION_DATA                 0x3D /**< 3D Information Data. */
#define BLE_GAP_AD_TYPE_MANUFACTURER_SPECIFIC_DATA          0xFF /**< Manufacturer Specific Data. */
/**@} */


/**@defgroup BLE_GAP_ADV_FLAGS GAP Advertisement Flags
 * @{ */
#define BLE_GAP_ADV_FLAG_LE_LIMITED_DISC_MODE         (0x01)   /**< LE Limited Discoverable Mode. */
#define BLE_GAP_ADV_FLAG_LE_GENERAL_DISC_MODE         (0x02)   /**< LE General Discoverable Mode. */
#define BLE_GAP_ADV_FLAG_BR_EDR_NOT_SUPPORTED         (0x04)   /**< BR/EDR not supported. */
#define BLE_GAP_ADV_FLAG_LE_BR_EDR_CONTROLLER         (0x08)   /**< Simultaneous LE and BR/EDR, Controller. */
#define BLE_GAP_ADV_FLAG_LE_BR_EDR_HOST               (0x10)   /**< Simultaneous LE and BR/EDR, Host. */
#define BLE_GAP_ADV_FLAGS_LE_ONLY_LIMITED_DISC_MODE   (BLE_GAP_ADV_FLAG_LE_LIMITED_DISC_MODE | BLE_GAP_ADV_FLAG_BR_EDR_NOT_SUPPORTED)   /**< LE Limited Discoverable Mode, BR/EDR not supported. */
#define BLE_GAP_ADV_FLAGS_LE_ONLY_GENERAL_DISC_MODE   (BLE_GAP_ADV_FLAG_LE_GENERAL_DISC_MODE | BLE_GAP_ADV_FLAG_BR_EDR_NOT_SUPPORTED)   /**< LE General Discoverable Mode, BR/EDR not supported. */
/**@} */


/**@defgroup BLE_GAP_ADV_INTERVALS GAP Advertising interval max and min
 * @{ */
#define BLE_GAP_ADV_INTERVAL_MIN        0x000020 /**< Minimum Advertising interval in 625 us units, i.e. 20 ms. */
#define BLE_GAP_ADV_INTERVAL_MAX        0x004000 /**< Maximum Advertising interval in 625 us units, i.e. 10.24 s. */
 /**@}  */


/**@defgroup BLE_GAP_SCAN_INTERVALS GAP Scan interval max and min
 * @{ */
#define BLE_GAP_SCAN_INTERVAL_MIN       0x0004 /**< Minimum Scan interval in 625 us units, i.e. 2.5 ms. */
#define BLE_GAP_SCAN_INTERVAL_MAX       0xFFFF /**< Maximum Scan interval in 625 us units, i.e. 40,959.375 s. */
 /** @}  */


/**@defgroup BLE_GAP_SCAN_WINDOW GAP Scan window max and min
 * @{ */
#define BLE_GAP_SCAN_WINDOW_MIN         0x0004 /**< Minimum Scan window in 625 us units, i.e. 2.5 ms. */
#define BLE_GAP_SCAN_WINDOW_MAX         0xFFFF /**< Maximum Scan window in 625 us units, i.e. 40,959.375 s. */
 /** @}  */


/**@defgroup BLE_GAP_SCAN_TIMEOUT GAP Scan timeout max and min
 * @{ */
#define BLE_GAP_SCAN_TIMEOUT_MIN        0x0001 /**< Minimum Scan timeout in 10 ms units, i.e 10 ms. */
#define BLE_GAP_SCAN_TIMEOUT_UNLIMITED  0x0000 /**< Continue to scan forever. */
 /** @}  */

/**@defgroup BLE_GAP_SCAN_BUFFER_SIZE GAP Minimum scanner buffer size
 *
 * Scan buffers are used for storing advertising data received from an advertiser.
 * If ble_gap_scan_params_t::extended is set to 0, @ref BLE_GAP_SCAN_BUFFER_MIN is the minimum scan buffer length.
 * else the minimum scan buffer size is @ref BLE_GAP_SCAN_BUFFER_EXTENDED_MIN.
 * @{ */
#define BLE_GAP_SCAN_BUFFER_MIN                    (31)                             /**< Minimum data length for an
                                                                                         advertising set. */
#define BLE_GAP_SCAN_BUFFER_MAX                    (31)                             /**< Maximum data length for an
                                                                                         advertising set. */
#define BLE_GAP_SCAN_BUFFER_EXTENDED_MIN           (255)                            /**< Minimum data length for an
                                                                                         extended advertising set. */
#define BLE_GAP_SCAN_BUFFER_EXTENDED_MAX           (1650)                           /**< Maximum data length for an
                                                                                         extended advertising set. */
#define BLE_GAP_SCAN_BUFFER_EXTENDED_MAX_SUPPORTED (255)                            /**< Maximum supported data length for
                                                                                         an extended advertising set. */
/** @}  */

/**@defgroup BLE_GAP_ADV_TYPES GAP Advertising types
 *
 * Advertising types defined in Bluetooth Core Specification v5.0, Vol 6, Part B, Section 4.4.2.
 *
 * The maximum advertising data length is defined by @ref BLE_GAP_ADV_SET_DATA_SIZE_MAX.
 * The maximum supported data length for an extended advertiser is defined by
 * @ref BLE_GAP_ADV_SET_DATA_SIZE_EXTENDED_MAX_SUPPORTED
 * Note that some of the advertising types do not support advertising data. Non-scannable types do not support
 * scan response data.
 *
 * @{ */
#define BLE_GAP_ADV_TYPE_CONNECTABLE_SCANNABLE_UNDIRECTED                   0x01   /**< Connectable and scannable undirected
                                                                                        advertising events. */
#define BLE_GAP_ADV_TYPE_CONNECTABLE_NONSCANNABLE_DIRECTED_HIGH_DUTY_CYCLE  0x02   /**< Connectable non-scannable directed advertising
                                                                                        events. Advertising interval is less that 3.75 ms.
                                                                                        Use this type for fast reconnections.
                                                                                        @note Advertising data is not supported. */
#define BLE_GAP_ADV_TYPE_CONNECTABLE_NONSCANNABLE_DIRECTED                  0x03   /**< Connectable non-scannable directed advertising
                                                                                        events.
                                                                                        @note Advertising data is not supported. */
#define BLE_GAP_ADV_TYPE_NONCONNECTABLE_SCANNABLE_UNDIRECTED                0x04   /**< Non-connectable scannable undirected
                                                                                        advertising events. */
#define BLE_GAP_ADV_TYPE_NONCONNECTABLE_NONSCANNABLE_UNDIRECTED             0x05   /**< Non-connectable non-scannable undirected
                                                                                        advertising events. */
#define BLE_GAP_ADV_TYPE_EXTENDED_CONNECTABLE_NONSCANNABLE_UNDIRECTED       0x06   /**< Connectable non-scannable undirected advertising
                                                                                        events using extended advertising PDUs. */
#define BLE_GAP_ADV_TYPE_EXTENDED_CONNECTABLE_NONSCANNABLE_DIRECTED         0x07   /**< Connectable non-scannable directed advertising
                                                                                        events using extended advertising PDUs. */
#define BLE_GAP_ADV_TYPE_EXTENDED_NONCONNECTABLE_SCANNABLE_UNDIRECTED       0x08   /**< Non-connectable scannable undirected advertising
                                                                                        events using extended advertising PDUs.
                                                                                        @note Only scan response data is supported. */
#define BLE_GAP_ADV_TYPE_EXTENDED_NONCONNECTABLE_SCANNABLE_DIRECTED         0x09   /**< Non-connectable scannable directed advertising
                                                                                        events using extended advertising PDUs.
                                                                                        @note Only scan response data is supported. */
#define BLE_GAP_ADV_TYPE_EXTENDED_NONCONNECTABLE_NONSCANNABLE_UNDIRECTED    0x0A   /**< Non-connectable non-scannable undirected advertising
                                                                                        events using extended advertising PDUs. */
#define BLE_GAP_ADV_TYPE_EXTENDED_NONCONNECTABLE_NONSCANNABLE_DIRECTED      0x0B   /**< Non-connectable non-scannable directed advertising
                                                                                        events using extended advertising PDUs. */
/**@} */

/**@defgroup BLE_GAP_ADV_FILTER_POLICIES GAP Advertising filter policies
 * @{ */
#define BLE_GAP_ADV_FP_ANY                0x00   /**< Allow scan requests and connect requests from any device. */
#define BLE_GAP_ADV_FP_FILTER_SCANREQ     0x01   /**< Filter scan requests with whitelist. */
#define BLE_GAP_ADV_FP_FILTER_CONNREQ     0x02   /**< Filter connect requests with whitelist. */
#define BLE_GAP_ADV_FP_FILTER_BOTH        0x03   /**< Filter both scan and connect requests with whitelist. */
/**@} */

/**@defgroup BLE_GAP_ADV_DATA_STATUS GAP Advertising data status
 * @{ */
#define BLE_GAP_ADV_DATA_STATUS_COMPLETE             0x00 /**< All data in the advertising event have been received. */
#define BLE_GAP_ADV_DATA_STATUS_INCOMPLETE_MORE_DATA 0x01 /**< More data to be received.
                                                               @note This value will only be used if
                                                               @ref ble_gap_scan_params_t::report_incomplete_evts and
                                                               @ref ble_gap_adv_report_type_t::extended_pdu are set to true. */
#define BLE_GAP_ADV_DATA_STATUS_INCOMPLETE_TRUNCATED 0x02 /**< Incomplete data. Buffer size insufficient to receive more.
                                                               @note This value will only be used if
                                                               @ref ble_gap_adv_report_type_t::extended_pdu is set to true. */
#define BLE_GAP_ADV_DATA_STATUS_INCOMPLETE_MISSED    0x03 /**< Failed to receive the remaining data.
                                                               @note This value will only be used if
                                                               @ref ble_gap_adv_report_type_t::extended_pdu is set to true. */
/**@} */

/**@defgroup BLE_GAP_SCAN_FILTER_POLICIES GAP Scanner filter policies
 * @{ */
#define BLE_GAP_SCAN_FP_ACCEPT_ALL                      0x00  /**< Accept all advertising packets except directed advertising packets
                                                                   not addressed to this device. */
#define BLE_GAP_SCAN_FP_WHITELIST                       0x01  /**< Accept advertising packets from devices in the whitelist except directed
                                                                   packets not addressed to this device. */
#define BLE_GAP_SCAN_FP_ALL_NOT_RESOLVED_DIRECTED       0x02  /**< Accept all advertising packets specified in @ref BLE_GAP_SCAN_FP_ACCEPT_ALL.
                                                                   In addition, accept directed advertising packets, where the advertiser's
                                                                   address is a resolvable private address that cannot be resolved. */
#define BLE_GAP_SCAN_FP_WHITELIST_NOT_RESOLVED_DIRECTED 0x03  /**< Accept all advertising packets specified in @ref BLE_GAP_SCAN_FP_WHITELIST.
                                                                   In addition, accept directed advertising packets, where the advertiser's
                                                                   address is a resolvable private address that cannot be resolved. */
/**@} */

/**@defgroup BLE_GAP_ADV_TIMEOUT_VALUES GAP Advertising timeout values in 10 ms units
 * @{ */
#define BLE_GAP_ADV_TIMEOUT_HIGH_DUTY_MAX     (128)   /**< Maximum high duty advertising time in 10 ms units. Corresponds to 1.28 s. */
#define BLE_GAP_ADV_TIMEOUT_LIMITED_MAX       (18000) /**< Maximum advertising time in 10 ms units corresponding to TGAP(lim_adv_timeout) = 180 s in limited discoverable mode. */
#define BLE_GAP_ADV_TIMEOUT_GENERAL_UNLIMITED (0)     /**< Unlimited advertising in general discoverable mode.
                                                           For high duty cycle advertising, this corresponds to @ref BLE_GAP_ADV_TIMEOUT_HIGH_DUTY_MAX. */
/**@} */


/**@defgroup BLE_GAP_DISC_MODES GAP Discovery modes
 * @{ */
#define BLE_GAP_DISC_MODE_NOT_DISCOVERABLE  0x00   /**< Not discoverable discovery Mode. */
#define BLE_GAP_DISC_MODE_LIMITED           0x01   /**< Limited Discovery Mode. */
#define BLE_GAP_DISC_MODE_GENERAL           0x02   /**< General Discovery Mode. */
/**@} */


/**@defgroup BLE_GAP_IO_CAPS GAP IO Capabilities
 * @{ */
#define BLE_GAP_IO_CAPS_DISPLAY_ONLY      0x00   /**< Display Only. */
#define BLE_GAP_IO_CAPS_DISPLAY_YESNO     0x01   /**< Display and Yes/No entry. */
#define BLE_GAP_IO_CAPS_KEYBOARD_ONLY     0x02   /**< Keyboard Only. */
#define BLE_GAP_IO_CAPS_NONE              0x03   /**< No I/O capabilities. */
#define BLE_GAP_IO_CAPS_KEYBOARD_DISPLAY  0x04   /**< Keyboard and Display. */
/**@} */


/**@defgroup BLE_GAP_AUTH_KEY_TYPES GAP Authentication Key Types
 * @{ */
#define BLE_GAP_AUTH_KEY_TYPE_NONE        0x00   /**< No key (may be used to reject). */
#define BLE_GAP_AUTH_KEY_TYPE_PASSKEY     0x01   /**< 6-digit Passkey. */
#define BLE_GAP_AUTH_KEY_TYPE_OOB         0x02   /**< Out Of Band data. */
/**@} */


/**@defgroup BLE_GAP_KP_NOT_TYPES GAP Keypress Notification Types
 * @{ */
#define BLE_GAP_KP_NOT_TYPE_PASSKEY_START       0x00   /**< Passkey entry started. */
#define BLE_GAP_KP_NOT_TYPE_PASSKEY_DIGIT_IN    0x01   /**< Passkey digit entered. */
#define BLE_GAP_KP_NOT_TYPE_PASSKEY_DIGIT_OUT   0x02   /**< Passkey digit erased. */
#define BLE_GAP_KP_NOT_TYPE_PASSKEY_CLEAR       0x03   /**< Passkey cleared. */
#define BLE_GAP_KP_NOT_TYPE_PASSKEY_END         0x04   /**< Passkey entry completed. */
/**@} */


/**@defgroup BLE_GAP_SEC_STATUS GAP Security status
 * @{ */
#define BLE_GAP_SEC_STATUS_SUCCESS                0x00  /**< Procedure completed with success. */
#define BLE_GAP_SEC_STATUS_TIMEOUT                0x01  /**< Procedure timed out. */
#define BLE_GAP_SEC_STATUS_PDU_INVALID            0x02  /**< Invalid PDU received. */
#define BLE_GAP_SEC_STATUS_RFU_RANGE1_BEGIN       0x03  /**< Reserved for Future Use range #1 begin. */
#define BLE_GAP_SEC_STATUS_RFU_RANGE1_END         0x80  /**< Reserved for Future Use range #1 end. */
#define BLE_GAP_SEC_STATUS_PASSKEY_ENTRY_FAILED   0x81  /**< Passkey entry failed (user canceled or other). */
#define BLE_GAP_SEC_STATUS_OOB_NOT_AVAILABLE      0x82  /**< Out of Band Key not available. */
#define BLE_GAP_SEC_STATUS_AUTH_REQ               0x83  /**< Authentication requirements not met. */
#define BLE_GAP_SEC_STATUS_CONFIRM_VALUE          0x84  /**< Confirm value failed. */
#define BLE_GAP_SEC_STATUS_PAIRING_NOT_SUPP       0x85  /**< Pairing not supported.  */
#define BLE_GAP_SEC_STATUS_ENC_KEY_SIZE           0x86  /**< Encryption key size. */
#define BLE_GAP_SEC_STATUS_SMP_CMD_UNSUPPORTED    0x87  /**< Unsupported SMP command. */
#define BLE_GAP_SEC_STATUS_UNSPECIFIED            0x88  /**< Unspecified reason. */
#define BLE_GAP_SEC_STATUS_REPEATED_ATTEMPTS      0x89  /**< Too little time elapsed since last attempt. */
#define BLE_GAP_SEC_STATUS_INVALID_PARAMS         0x8A  /**< Invalid parameters. */
#define BLE_GAP_SEC_STATUS_DHKEY_FAILURE          0x8B  /**< DHKey check failure. */
#define BLE_GAP_SEC_STATUS_NUM_COMP_FAILURE       0x8C  /**< Numeric Comparison failure. */
#define BLE_GAP_SEC_STATUS_BR_EDR_IN_PROG         0x8D  /**< BR/EDR pairing in progress. */
#define BLE_GAP_SEC_STATUS_X_TRANS_KEY_DISALLOWED 0x8E  /**< BR/EDR Link Key cannot be used for LE keys. */
#define BLE_GAP_SEC_STATUS_RFU_RANGE2_BEGIN       0x8F  /**< Reserved for Future Use range #2 begin. */
#define BLE_GAP_SEC_STATUS_RFU_RANGE2_END         0xFF  /**< Reserved for Future Use range #2 end. */
/**@} */


/**@defgroup BLE_GAP_SEC_STATUS_SOURCES GAP Security status sources
 * @{ */
#define BLE_GAP_SEC_STATUS_SOURCE_LOCAL           0x00  /**< Local failure. */
#define BLE_GAP_SEC_STATUS_SOURCE_REMOTE          0x01  /**< Remote failure. */
/**@} */


/**@defgroup BLE_GAP_CP_LIMITS GAP Connection Parameters Limits
 * @{ */
#define BLE_GAP_CP_MIN_CONN_INTVL_NONE           0xFFFF  /**< No new minimum connection interval specified in connect parameters. */
#define BLE_GAP_CP_MIN_CONN_INTVL_MIN            0x0006  /**< Lowest minimum connection interval permitted, in units of 1.25 ms, i.e. 7.5 ms. */
#define BLE_GAP_CP_MIN_CONN_INTVL_MAX            0x0C80  /**< Highest minimum connection interval permitted, in units of 1.25 ms, i.e. 4 s. */
#define BLE_GAP_CP_MAX_CONN_INTVL_NONE           0xFFFF  /**< No new maximum connection interval specified in connect parameters. */
#define BLE_GAP_CP_MAX_CONN_INTVL_MIN            0x0006  /**< Lowest maximum connection interval permitted, in units of 1.25 ms, i.e. 7.5 ms. */
#define BLE_GAP_CP_MAX_CONN_INTVL_MAX            0x0C80  /**< Highest maximum connection interval permitted, in units of 1.25 ms, i.e. 4 s. */
#define BLE_GAP_CP_SLAVE_LATENCY_MAX             0x01F3  /**< Highest slave latency permitted, in connection events. */
#define BLE_GAP_CP_CONN_SUP_TIMEOUT_NONE         0xFFFF  /**< No new supervision timeout specified in connect parameters. */
#define BLE_GAP_CP_CONN_SUP_TIMEOUT_MIN          0x000A  /**< Lowest supervision timeout permitted, in units of 10 ms, i.e. 100 ms. */
#define BLE_GAP_CP_CONN_SUP_TIMEOUT_MAX          0x0C80  /**< Highest supervision timeout permitted, in units of 10 ms, i.e. 32 s. */
/**@} */


/**@defgroup BLE_GAP_DEVNAME GAP device name defines.
 * @{ */
#define BLE_GAP_DEVNAME_DEFAULT                  "nRF5x" /**< Default device name value. */
#define BLE_GAP_DEVNAME_DEFAULT_LEN              31      /**< Default number of octets in device name. */
#define BLE_GAP_DEVNAME_MAX_LEN                  248     /**< Maximum number of octets in device name. */
/**@} */


/**@brief Disable RSSI events for connections */
#define BLE_GAP_RSSI_THRESHOLD_INVALID 0xFF

/**@defgroup BLE_GAP_PHYS GAP PHYs
 * @{ */
#define BLE_GAP_PHY_AUTO                         0x00    /**< Automatic PHY selection. Refer @ref sd_ble_gap_phy_update for more information.*/
#define BLE_GAP_PHY_1MBPS                        0x01    /**< 1 Mbps PHY. */
#define BLE_GAP_PHY_2MBPS                        0x02    /**< 2 Mbps PHY. */
#define BLE_GAP_PHY_CODED                        0x04    /**< Coded PHY. */
#define BLE_GAP_PHY_NOT_SET                      0xFF    /**< PHY is not configured. */

/**@brief Supported PHYs in connections, for scanning, and for advertising. */
#define BLE_GAP_PHYS_SUPPORTED  (BLE_GAP_PHY_1MBPS | BLE_GAP_PHY_2MBPS) /**< All PHYs except @ref BLE_GAP_PHY_CODED are supported. */

/**@} */

/**@defgroup BLE_GAP_CONN_SEC_MODE_SET_MACROS GAP attribute security requirement setters
 *
 * See @ref ble_gap_conn_sec_mode_t.
 * @{ */
/**@brief Set sec_mode pointed to by ptr to have no access rights.*/
#define BLE_GAP_CONN_SEC_MODE_SET_NO_ACCESS(ptr)          do {(ptr)->sm = 0; (ptr)->lv = 0;} while(0)
/**@brief Set sec_mode pointed to by ptr to require no protection, open link.*/
#define BLE_GAP_CONN_SEC_MODE_SET_OPEN(ptr)               do {(ptr)->sm = 1; (ptr)->lv = 1;} while(0)
/**@brief Set sec_mode pointed to by ptr to require encryption, but no MITM protection.*/
#define BLE_GAP_CONN_SEC_MODE_SET_ENC_NO_MITM(ptr)        do {(ptr)->sm = 1; (ptr)->lv = 2;} while(0)
/**@brief Set sec_mode pointed to by ptr to require encryption and MITM protection.*/
#define BLE_GAP_CONN_SEC_MODE_SET_ENC_WITH_MITM(ptr)      do {(ptr)->sm = 1; (ptr)->lv = 3;} while(0)
/**@brief Set sec_mode pointed to by ptr to require LESC encryption and MITM protection.*/
#define BLE_GAP_CONN_SEC_MODE_SET_LESC_ENC_WITH_MITM(ptr) do {(ptr)->sm = 1; (ptr)->lv = 4;} while(0)
/**@brief Set sec_mode pointed to by ptr to require signing or encryption, no MITM protection needed.*/
#define BLE_GAP_CONN_SEC_MODE_SET_SIGNED_NO_MITM(ptr)     do {(ptr)->sm = 2; (ptr)->lv = 1;} while(0)
/**@brief Set sec_mode pointed to by ptr to require signing or encryption with MITM protection.*/
#define BLE_GAP_CONN_SEC_MODE_SET_SIGNED_WITH_MITM(ptr)   do {(ptr)->sm = 2; (ptr)->lv = 2;} while(0)
/**@} */


/**@brief GAP Security Random Number Length. */
#define BLE_GAP_SEC_RAND_LEN 8


/**@brief GAP Security Key Length. */
#define BLE_GAP_SEC_KEY_LEN 16


/**@brief GAP LE Secure Connections Elliptic Curve Diffie-Hellman P-256 Public Key Length. */
#define BLE_GAP_LESC_P256_PK_LEN 64


/**@brief GAP LE Secure Connections Elliptic Curve Diffie-Hellman DHKey Length. */
#define BLE_GAP_LESC_DHKEY_LEN   32


/**@brief GAP Passkey Length. */
#define BLE_GAP_PASSKEY_LEN 6


/**@brief Maximum amount of addresses in the whitelist. */
#define BLE_GAP_WHITELIST_ADDR_MAX_COUNT (8)


/**@brief Maximum amount of identities in the device identities list. */
#define BLE_GAP_DEVICE_IDENTITIES_MAX_COUNT (8)


/**@brief Default connection count for a configuration. */
#define BLE_GAP_CONN_COUNT_DEFAULT (1)


/**@defgroup BLE_GAP_EVENT_LENGTH GAP event length defines.
 * @{ */
#define BLE_GAP_EVENT_LENGTH_MIN            (2)  /**< Minimum event length, in 1.25 ms units. */
#define BLE_GAP_EVENT_LENGTH_DEFAULT        (3)  /**< Default event length, in 1.25 ms units. */
/**@} */


/**@defgroup BLE_GAP_ROLE_COUNT GAP concurrent connection count defines.
 * @{ */
#define BLE_GAP_ROLE_COUNT_PERIPH_DEFAULT      (1)   /**< Default maximum number of connections concurrently acting as peripherals. */
#define BLE_GAP_ROLE_COUNT_CENTRAL_DEFAULT     (3)   /**< Default maximum number of connections concurrently acting as centrals. */
#define BLE_GAP_ROLE_COUNT_CENTRAL_SEC_DEFAULT (1)   /**< Default number of SMP instances shared between all connections acting as centrals. */
#define BLE_GAP_ROLE_COUNT_COMBINED_MAX        (20)  /**< Maximum supported number of concurrent connections in the peripheral and central roles combined. */

/**@} */

/**@brief Automatic data length parameter. */
#define BLE_GAP_DATA_LENGTH_AUTO 0

/**@defgroup BLE_GAP_AUTH_PAYLOAD_TIMEOUT Authenticated payload timeout defines.
  * @{ */
#define BLE_GAP_AUTH_PAYLOAD_TIMEOUT_MAX (48000) /**< Maximum authenticated payload timeout in 10 ms units, i.e. 8 minutes. */
#define BLE_GAP_AUTH_PAYLOAD_TIMEOUT_MIN (1)     /**< Minimum authenticated payload timeout in 10 ms units, i.e. 10 ms. */
/**@} */

/**@defgroup GAP_SEC_MODES GAP Security Modes
 * @{ */
#define BLE_GAP_SEC_MODE 0x00 /**< No key (may be used to reject). */
/**@} */

/**@brief The total number of channels in Bluetooth Low Energy. */
#define BLE_GAP_CHANNEL_COUNT      (40)

/**@defgroup BLE_GAP_QOS_CHANNEL_SURVEY_INTERVALS Quality of Service (QoS) Channel survey interval defines
 * @{ */
#define BLE_GAP_QOS_CHANNEL_SURVEY_INTERVAL_CONTINUOUS  (0)       /**< Continuous channel survey. */
#define BLE_GAP_QOS_CHANNEL_SURVEY_INTERVAL_MIN_US      (7500)    /**< Minimum channel survey interval in microseconds (7.5 ms). */
#define BLE_GAP_QOS_CHANNEL_SURVEY_INTERVAL_MAX_US      (4000000) /**< Maximum channel survey interval in microseconds (4 s). */
 /**@}  */

/** @} */


/**@addtogroup BLE_GAP_STRUCTURES Structures
 * @{ */

/**@brief Advertising event properties. */
typedef struct
{
  uint8_t type;                 /**< Advertising type. See @ref BLE_GAP_ADV_TYPES. */
  uint8_t anonymous        : 1; /**< Omit advertiser's address from all PDUs.
                                     @note Anonymous advertising is only available for
                                     @ref BLE_GAP_ADV_TYPE_EXTENDED_NONCONNECTABLE_NONSCANNABLE_UNDIRECTED and
                                     @ref BLE_GAP_ADV_TYPE_EXTENDED_NONCONNECTABLE_NONSCANNABLE_DIRECTED. */
  uint8_t include_tx_power : 1; /**< This feature is not supported on this SoftDevice. */
} ble_gap_adv_properties_t;


/**@brief Advertising report type. */
typedef struct
{
  uint16_t connectable   : 1; /**< Connectable advertising event type. */
  uint16_t scannable     : 1; /**< Scannable advertising event type. */
  uint16_t directed      : 1; /**< Directed advertising event type. */
  uint16_t scan_response : 1; /**< Received a scan response. */
  uint16_t extended_pdu  : 1; /**< Received an extended advertising set. */
  uint16_t status        : 2; /**< Data status. See @ref BLE_GAP_ADV_DATA_STATUS. */
  uint16_t reserved      : 9; /**< Reserved for future use. */
} ble_gap_adv_report_type_t;

/**@brief Advertising Auxiliary Pointer. */
typedef struct
{
  uint16_t  aux_offset;   /**< Time offset from the beginning of advertising packet to the auxiliary packet in 100 us units. */
  uint8_t   aux_phy;      /**< Indicates the PHY on which the auxiliary advertising packet is sent. See @ref BLE_GAP_PHYS. */
} ble_gap_aux_pointer_t;

/**@brief Bluetooth Low Energy address. */
typedef struct
{
  uint8_t addr_id_peer : 1;       /**< Only valid for peer addresses.
                                       This bit is set by the SoftDevice to indicate whether the address has been resolved from
                                       a Resolvable Private Address (when the peer is using privacy).
                                       If set to 1, @ref addr and @ref addr_type refer to the identity address of the resolved address.

                                       This bit is ignored when a variable of type @ref ble_gap_addr_t is used as input to API functions. */
  uint8_t addr_type    : 7;       /**< See @ref BLE_GAP_ADDR_TYPES. */
  uint8_t addr[BLE_GAP_ADDR_LEN]; /**< 48-bit address, LSB format.
                                       @ref addr is not used if @ref addr_type is @ref BLE_GAP_ADDR_TYPE_ANONYMOUS. */
} ble_gap_addr_t;


/**@brief GAP connection parameters.
 *
 * @note  When ble_conn_params_t is received in an event, both min_conn_interval and
 *        max_conn_interval will be equal to the connection interval set by the central.
 *
 * @note  If both conn_sup_timeout and max_conn_interval are specified, then the following constraint applies:
 *        conn_sup_timeout * 4 > (1 + slave_latency) * max_conn_interval
 *        that corresponds to the following Bluetooth Spec requirement:
 *        The Supervision_Timeout in milliseconds shall be larger than
 *        (1 + Conn_Latency) * Conn_Interval_Max * 2, where Conn_Interval_Max is given in milliseconds.
 */
typedef struct
{
  uint16_t min_conn_interval;         /**< Minimum Connection Interval in 1.25 ms units, see @ref BLE_GAP_CP_LIMITS.*/
  uint16_t max_conn_interval;         /**< Maximum Connection Interval in 1.25 ms units, see @ref BLE_GAP_CP_LIMITS.*/
  uint16_t slave_latency;             /**< Slave Latency in number of connection events, see @ref BLE_GAP_CP_LIMITS.*/
  uint16_t conn_sup_timeout;          /**< Connection Supervision Timeout in 10 ms units, see @ref BLE_GAP_CP_LIMITS.*/
} ble_gap_conn_params_t;


/**@brief GAP connection security modes.
 *
 * Security Mode 0 Level 0: No access permissions at all (this level is not defined by the Bluetooth Core specification).\n
 * Security Mode 1 Level 1: No security is needed (aka open link).\n
 * Security Mode 1 Level 2: Encrypted link required, MITM protection not necessary.\n
 * Security Mode 1 Level 3: MITM protected encrypted link required.\n
 * Security Mode 1 Level 4: LESC MITM protected encrypted link using a 128-bit strength encryption key required.\n
 * Security Mode 2 Level 1: Signing or encryption required, MITM protection not necessary.\n
 * Security Mode 2 Level 2: MITM protected signing required, unless link is MITM protected encrypted.\n
 */
typedef struct
{
  uint8_t sm : 4;                     /**< Security Mode (1 or 2), 0 for no permissions at all. */
  uint8_t lv : 4;                     /**< Level (1, 2, 3 or 4), 0 for no permissions at all. */

} ble_gap_conn_sec_mode_t;


/**@brief GAP connection security status.*/
typedef struct
{
  ble_gap_conn_sec_mode_t sec_mode;           /**< Currently active security mode for this connection.*/
  uint8_t                 encr_key_size;      /**< Length of currently active encryption key, 7 to 16 octets (only applicable for bonding procedures). */
} ble_gap_conn_sec_t;

/**@brief Identity Resolving Key. */
typedef struct
{
  uint8_t irk[BLE_GAP_SEC_KEY_LEN];   /**< Array containing IRK. */
} ble_gap_irk_t;


/**@brief Channel mask (40 bits).
 * Every channel is represented with a bit positioned as per channel index defined in Bluetooth Core Specification v5.0,
 * Vol 6, Part B, Section 1.4.1. The LSB contained in array element 0 represents channel index 0, and bit 39 represents
 * channel index 39. If a bit is set to 1, the channel is not used.
 */
typedef uint8_t ble_gap_ch_mask_t[5];


/**@brief GAP advertising parameters. */
typedef struct
{
  ble_gap_adv_properties_t properties;              /**< The properties of the advertising events. */
  ble_gap_addr_t const    *p_peer_addr;             /**< Address of a known peer.
                                                         @note ble_gap_addr_t::addr_type cannot be
                                                               @ref BLE_GAP_ADDR_TYPE_ANONYMOUS.
                                                         - When privacy is enabled and the local device uses
                                                           @ref BLE_GAP_ADDR_TYPE_RANDOM_PRIVATE_RESOLVABLE addresses,
                                                           the device identity list is searched for a matching entry. If
                                                           the local IRK for that device identity is set, the local IRK
                                                           for that device will be used to generate the advertiser address
                                                           field in the advertising packet.
                                                         - If @ref ble_gap_adv_properties_t::type is directed, this must be
                                                           set to the targeted scanner or initiator. If the peer address is
                                                           in the device identity list, the peer IRK for that device will be
                                                           used to generate @ref BLE_GAP_ADDR_TYPE_RANDOM_PRIVATE_RESOLVABLE
                                                           target addresses used in the advertising event PDUs. */
  uint32_t                 interval;                /**< Advertising interval in 625 us units. @sa BLE_GAP_ADV_INTERVALS.
                                                         @note If @ref ble_gap_adv_properties_t::type is set to
                                                               @ref BLE_GAP_ADV_TYPE_CONNECTABLE_NONSCANNABLE_DIRECTED_HIGH_DUTY_CYCLE
                                                               advertising, this parameter is ignored. */
  uint16_t                 duration;                /**< Advertising duration in 10 ms units. When timeout is reached,
                                                         an event of type @ref BLE_GAP_EVT_ADV_SET_TERMINATED is raised.
                                                         @sa BLE_GAP_ADV_TIMEOUT_VALUES.
                                                         @note The SoftDevice will always complete at least one advertising
                                                               event even if the duration is set too low. */
  uint8_t                  max_adv_evts;            /**< Maximum advertising events that shall be sent prior to disabling
                                                         advertising. Setting the value to 0 disables the limitation. When
                                                         the count of advertising events specified by this parameter
                                                         (if not 0) is reached, advertising will be automatically stopped
                                                         and an event of type @ref BLE_GAP_EVT_ADV_SET_TERMINATED is raised
                                                         @note If @ref ble_gap_adv_properties_t::type is set to
                                                               @ref BLE_GAP_ADV_TYPE_CONNECTABLE_NONSCANNABLE_DIRECTED_HIGH_DUTY_CYCLE,
                                                               this parameter is ignored. */
  ble_gap_ch_mask_t        channel_mask;            /**< Channel mask for primary and secondary advertising channels.
                                                         At least one of the primary channels, that is channel index 37-39, must be used.
                                                         Masking away secondary advertising channels is not supported. */
  uint8_t                  filter_policy;           /**< Filter Policy. @sa BLE_GAP_ADV_FILTER_POLICIES. */
  uint8_t                  primary_phy;             /**< Indicates the PHY on which the primary advertising channel packets
                                                         are transmitted. If set to @ref BLE_GAP_PHY_AUTO, @ref BLE_GAP_PHY_1MBPS
                                                         will be used.
                                                         The only supported value by this SoftDevice is @ref BLE_GAP_PHY_1MBPS. */
  uint8_t                  secondary_phy;           /**< Indicates the PHY on which the secondary advertising channel packets
                                                         are transmitted.
                                                         If set to @ref BLE_GAP_PHY_AUTO, @ref BLE_GAP_PHY_1MBPS will be used.
                                                         Valid values are
                                                         @ref BLE_GAP_PHY_1MBPS and @ref BLE_GAP_PHY_2MBPS. @ref BLE_GAP_PHY_CODED
                                                         is not supported by this SoftDevice.
                                                         If @ref ble_gap_adv_properties_t::type is an extended advertising type
                                                         and connectable, this is the PHY that will be used to establish a
                                                         connection and send AUX_ADV_IND packets on.
                                                         @note This parameter will be ignored when
                                                               @ref ble_gap_adv_properties_t::type is not an extended advertising type. */
  uint8_t                  set_id:4;                /**< The advertising set identifier distinguishes this advertising set from other
                                                         advertising sets transmitted by this and other devices.
                                                         @note This parameter will be ignored when
                                                               @ref ble_gap_adv_properties_t::type is not an extended advertising type. */
  uint8_t                  scan_req_notification:1; /**< Enable scan request notifications for this advertising set. When a
                                                         scan request is received and the scanner address is allowed
                                                         by the filter policy, @ref BLE_GAP_EVT_SCAN_REQ_REPORT is raised.
                                                         @note This parameter will be ignored when
                                                               @ref ble_gap_adv_properties_t::type is a non-scannable
                                                               advertising type. */
} ble_gap_adv_params_t;


/**@brief GAP advertising data buffers.
 *
 * The application must provide the buffers for advertisement. The memory shall reside in application RAM, and
 * shall never be modified while advertising. The data shall be kept alive until either:
 *  - @ref BLE_GAP_EVT_ADV_SET_TERMINATED is raised.
 *  - @ref BLE_GAP_EVT_CONNECTED is raised with @ref ble_gap_evt_connected_t::adv_handle set to the corresponding
 *    advertising handle.
 *  - Advertising is stopped.
 *  - Advertising data is changed.
 * To update advertising data while advertising, provide new buffers to @ref sd_ble_gap_adv_set_configure. */
typedef struct
{
  ble_data_t       adv_data;                     /**< Advertising data.
                                                      @note
                                                      Advertising data can only be specified for a @ref ble_gap_adv_properties_t::type
                                                      that is allowed to contain advertising data. */
  ble_data_t       scan_rsp_data;                /**< Scan response data.
                                                      @note
                                                      Scan response data can only be specified for a @ref ble_gap_adv_properties_t::type
                                                      that is scannable. */
} ble_gap_adv_data_t;


/**@brief GAP scanning parameters. */
typedef struct
{
  uint8_t               extended               : 1; /**< If 1, the scanner will accept extended advertising packets.
                                                         If set to 0, the scanner will not receive advertising packets
                                                         on secondary advertising channels, and will not be able
                                                         to receive long advertising PDUs. */
  uint8_t               report_incomplete_evts : 1; /**< If 1, events of type @ref ble_gap_evt_adv_report_t may have
                                                         @ref ble_gap_adv_report_type_t::status set to
                                                         @ref BLE_GAP_ADV_DATA_STATUS_INCOMPLETE_MORE_DATA.
                                                         This parameter is ignored when used with @ref sd_ble_gap_connect
                                                         @note This may be used to abort receiving more packets from an extended
                                                               advertising event, and is only available for extended
                                                               scanning, see @ref sd_ble_gap_scan_start.
                                                         @note This feature is not supported by this SoftDevice. */
  uint8_t               active                 : 1; /**< If 1, perform active scanning by sending scan requests.
                                                         This parameter is ignored when used with @ref sd_ble_gap_connect. */
  uint8_t               filter_policy          : 2; /**< Scanning filter policy. @sa BLE_GAP_SCAN_FILTER_POLICIES.
                                                         @note Only @ref BLE_GAP_SCAN_FP_ACCEPT_ALL and
                                                               @ref BLE_GAP_SCAN_FP_WHITELIST are valid when used with
                                                               @ref sd_ble_gap_connect */
  uint8_t               scan_phys;                  /**< Bitfield of PHYs to scan on. If set to @ref BLE_GAP_PHY_AUTO,
                                                         scan_phys will default to @ref BLE_GAP_PHY_1MBPS.
                                                         - If @ref ble_gap_scan_params_t::extended is set to 0, the only
                                                           supported PHY is @ref BLE_GAP_PHY_1MBPS.
                                                         - When used with @ref sd_ble_gap_scan_start,
                                                           the bitfield indicates the PHYs the scanner will use for scanning
                                                           on primary advertising channels. The scanner will accept
                                                           @ref BLE_GAP_PHYS_SUPPORTED as secondary advertising channel PHYs.
                                                         - When used with @ref sd_ble_gap_connect, the bitfield indicates
                                                           the PHYs the initiator will use for scanning on primary advertising
                                                           channels. The initiator will accept connections initiated on either
                                                           of the @ref BLE_GAP_PHYS_SUPPORTED PHYs.
                                                           If scan_phys contains @ref BLE_GAP_PHY_1MBPS and/or @ref BLE_GAP_PHY_2MBPS,
                                                           the primary scan PHY is @ref BLE_GAP_PHY_1MBPS. */
  uint16_t              interval;                   /**< Scan interval in 625 us units. @sa BLE_GAP_SCAN_INTERVALS. */
  uint16_t              window;                     /**< Scan window in 625 us units. @sa BLE_GAP_SCAN_WINDOW. */
  uint16_t              timeout;                    /**< Scan timeout in 10 ms units. @sa BLE_GAP_SCAN_TIMEOUT. */
  ble_gap_ch_mask_t     channel_mask;               /**< Channel mask for primary and secondary advertising channels.
                                                         At least one of the primary channels, that is channel index 37-39, must be
                                                         set to 0.
                                                         Masking away secondary channels is not supported. */
} ble_gap_scan_params_t;
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
