jeffc/nrf52-watch-obsolete/packages/framework-arduinoadafruitnrf52/cores/nRF5/wiring_analog_nRF52.c

/*
  Copyright (c) 2014 Arduino LLC.  All right reserved.
  Copyright (c) 2016 Sandeep Mistry All right reserved.

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
  You should have received a copy of the GNU Lesser General Public
  License along with this library; if not, write to the Free Software
  Foundation, Inc., 51 Franklin St, Fifth Floor, Boston, MA  02110-1301  USA
*/

#if defined(NRF52) || defined(NRF52_SERIES)

#include "nrf.h"

#include "Arduino.h"
#include "wiring_private.h"

#ifdef __cplusplus
extern "C" {
#endif

static uint32_t saadcReference = SAADC_CH_CONFIG_REFSEL_Internal;
static uint32_t saadcGain      = SAADC_CH_CONFIG_GAIN_Gain1_6;

static bool saadcBurst = SAADC_CH_CONFIG_BURST_Disabled;

#if 0 // Note: Adafruit use seperated HardwarePWM class
#define PWM_COUNT 3

static NRF_PWM_Type* pwms[PWM_COUNT] = {
  NRF_PWM0,
  NRF_PWM1,
  NRF_PWM2
};

static uint32_t pwmChannelPins[PWM_COUNT] = {
  0xFFFFFFFF,
  0xFFFFFFFF,
  0xFFFFFFFF
};
static uint16_t pwmChannelSequence[PWM_COUNT];
#endif

static int readResolution = 10;
//static int writeResolution = 8;

void analogReadResolution( int res )
{
  readResolution = res;
}

#if 0
void analogWriteResolution( int res )
{
  writeResolution = res;
}
#endif

static inline uint32_t mapResolution( uint32_t value, uint32_t from, uint32_t to )
{
  if ( from == to )
  {
    return value ;
  }

  if ( from > to )
  {
    return value >> (from-to) ;
  }
  else
  {
    return value << (to-from) ;
  }
}
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
